eigenlucy/micromppt/elec/src/parts/XySemi_XB3306D/SOT-23-3P_L2.9-W1.3-H1.0-LS2.4-P0.95.step

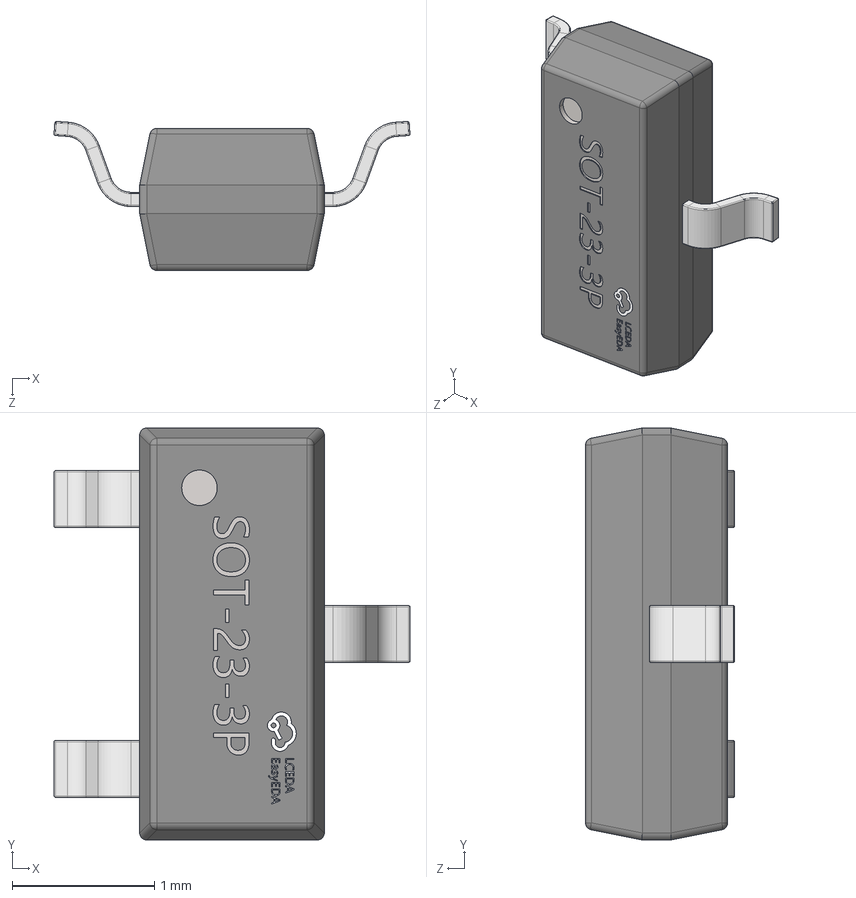
[picture p13: CAD file, 2025-03-08]
elec/src/parts/XySemi_XB3306D/SOT-23-3P_L2.9-W1.3-H1.0-LS2.4-P0.95.step
2.51 x 2.90 x 1.05 mm
